poempelfox/ledregenampel/espfw/main/defaultwifiappw.h

#ifndef _DEFWIFIAPPW_H_
#define _DEFWIFIAPPW_H_

/* This sets a password for the WiFi access point that
 * the firmware will open up for initial configuration.
 * You should absolutely set that, so you do not need to
 * do first-time configuration over unencrypted WiFi
 * with HTTP, thereby leaking secrets to anyone in WiFi
 * range.
 * Please note however that this setting will ONLY be
 * used if you have never changed ANY setting on the
 * device, i.e. there is no config section in the flash
 * at all.
 * If you comment out the define, the accesspoint will
 * be 'open'.
 */

#define DEFAULT_WIFI_AP_PW "regenampelconfig"

#endif /* _DEFWIFIAPPW_H_ */
